2024-Robocup-Soccer/Andys-Geese-2024/IR Sensor Hardware/Heat Maps/Sensor 1 With Shroud.png

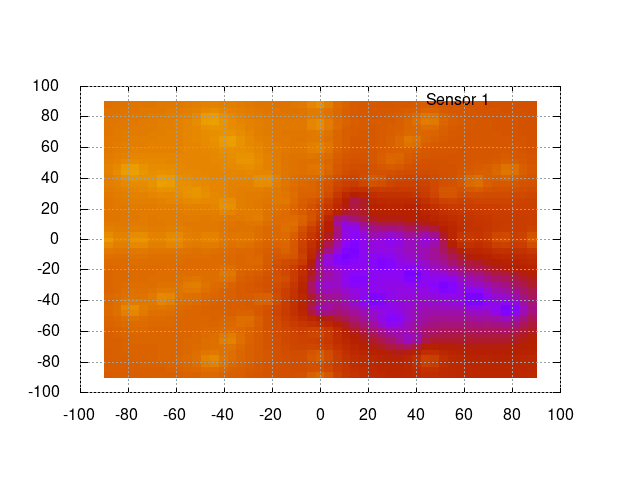
IR Sensor Hardware/Heat Maps/Sensor 1 With Shroud.png
