2024-Robocup-Soccer/Andys-Geese-2024/2024 Soccer/Working Code/colorSensorV2.h

#ifndef COLORSENSORV2_H
#define COLORSENSORV2_H

#include <Arduino.h>
#include <RunningMedian.h>

class ColorSensor {
public:
    ColorSensor();
    void init();
    int readSensor(int sensor);
    void readSensors();
    void fillMedians();
    float calculateDirection(); 
    void visualize();
    bool detectColor(int sensor);
    void calibrateSensors();
};

#endif
