2024-Robocup-Soccer/Andys-Geese-2024/2024 Soccer/Bottom Code/Compass.h

#ifndef COMPASS_H
#define COMPASS_H

#include <Arduino.h>

class Compass {
public: 
    Compass();
    void init();
    void initPrint();
    void resetCheck();
    void resetCheckPrint();
    float getBotAngle();
    
private:
    void setReports();
};

#endif
